aclandmark/PCB-111000/5_Clock_calibration/Resources/calibration subroutintes.c

void initialise_timers_for_cal_error(void);
void start_timers_for_cal_error(void);
long compute_error(char);	
long calibrate_quick_cal(char);
void start_T2_for_ATMEGA_168_cal(char);	
int compute_single_error(char, char);
int compute_single_error_signed(char, char);



		void initialise_timers_for_cal_error(void){
		TCNT1=0;TCCR1B = 0;								//Reset and halt T1
		TCCR2B =  0x0;	while(ASSR & (1 << TCR2BUB));	//Halt T2
		TCCR2A = 0; while(ASSR & (1 << TCR2AUB));		//Reset T2 
		TCNT2=0; while(ASSR & (1 << TCN2UB));	}		//Reset TCNT2

		
		void start_timers_for_cal_error(void)
		{TCCR2B = 1; 	
		while(ASSR & (1 << TCR2BUB));
		TCCR1B = 1;}							/////////////////////////////////////////////////
		
		long compute_error(char error_mode)//char OSCCAL_test_value)		
		{long error;
		EA_counter = 0;									//Compute error for each value of OSCCAL 10 times
		error_SUM = 0;
		while(EA_counter < 15);EA_counter = 0;
		error = error_SUM;
		if (error < 0) error *= (-1);
		if (error_mode){buffer[EA_buff_ptr] = error/10;EA_buff_ptr++;}
		return error/10;}
		
		
		long plot_cal_error(char error_mode)//char OSCCAL_test_value)		
		{long error;
		EA_counter = 0;									//Compute error for each value of OSCCAL 10 times
		error_SUM = 0;
		while(EA_counter < 2);{EA_counter = 0;}
		error = error_SUM;
		if (error_mode){buffer[EA_buff_ptr] = error;EA_buff_ptr++;}
		return error;}
		
		
		

		long calibrate_quick_cal(char OSCCAL_test)
		{long cal_error, error_mem;	
		OSCCAL = OSCCAL_test;		
		cal_error = compute_error(0);						//compute error for OSCCAL_test
		error_mem = cal_error;
		OSCCAL++;											//increment OSCALL
		while(1){
		cal_error = compute_error(0);						//Calculate new error
		if (cal_error > error_mem) { 										//If it gets worse
		OSCCAL--; break;}								//decrement OSCCAL and exit							
		error_mem = cal_error;							
		OSCCAL++;}
		if (OSCCAL != OSCCAL_test)	return error_mem;		//REPLACE with OSCCAL_DV when OSCCAL_test is discarded
		else{																//OSCCAL is still the default value
		OSCCAL--;
		while(1){
		cal_error = compute_error(0);
		if (cal_error > error_mem){ 										//If it gets worse
		OSCCAL++;
		break;}								//increment OSCCAL and exit
		error_mem = cal_error;							
		OSCCAL--;}}
		return error_mem;}
		
		
		int compute_single_error(char OSCCAL_TV, char OSCCAL_WV){		//Trial value
		int error;
		TIMSK2 |= (1 << TOIE2);								//Set Timer 2: interrupt on overflow
		TIMSK1 |= (1 << TOIE1);
		initialise_timers_for_cal_error();
		start_timers_for_cal_error();
		OSCCAL = OSCCAL_TV;
		error = compute_error(0);							//compute_single_error(m);
		error = compute_error(0);
		error = compute_error(0);
		OSCCAL = OSCCAL_WV;
		initialise_timers_for_cal_error();  				//dissable timers
		TIMSK2 &= (~(1 << TOIE2));							//Dissable Timer 2: interrupt on overflow
		TIMSK1 &= (~(1 << TOIE1));
		if(error < 0) error *= -1;
		return error;}
		
		
		
		int compute_single_error_signed(char OSCCAL_TV, char OSCCAL_WV){		//Trial value
		int error;
		TIMSK2 |= (1 << TOIE2);								//Set Timer 2: interrupt on overflow
		TIMSK1 |= (1 << TOIE1);
		initialise_timers_for_cal_error();
		start_timers_for_cal_error();
		OSCCAL = OSCCAL_TV;
		error = compute_error(0);							//compute_single_error(m);
		error = compute_error(0);
		error = compute_error(0);
		OSCCAL = OSCCAL_WV;
		initialise_timers_for_cal_error();  				//dissable timers
		TIMSK2 &= (~(1 << TOIE2));							//Dissable Timer 2: interrupt on overflow
		TIMSK1 &= (~(1 << TOIE1));
		return error;}
		
		
		
		
